kinetikalab/project_aetheris/results/50kHZ_DBD_FIP3200-24.jpg

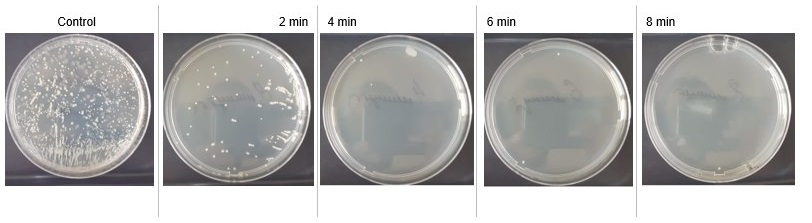
results/50kHZ_DBD_FIP3200-24.jpg
