kinetikalab/project_aetheris/power_electronics/equivalent_circuit/resonant_H_bridge.asc

C1: cap; 140n
Cd: cap; 15p
Cp: cap; 10p
Cw: cap; 9p
Lb: ind; {Lb}
Lm1: ind2; {Lm1}
Lm2: ind2; {Lm2}
Ls1: ind; {Ls1}
Ls2: ind; {Ls2}
R1: res; 10
Rd: res; 192000k
V1: voltage; SINE(0 19 550000); AC 1
Named nets: 0
K Lm1 Lm2 1
.ac oct 10000 10000 2000000
;.tran 1m
.param K1=0.995
.param Lm1 = L1*K1
.param Ls1 = L1*(1-K1)
.param Lm2 = L2*K1
.param Ls2 = L2*(1-K1)
.param L1=190u
.param L2=190m
.param Lb=10u
